prcoder-1/ATARI-SXEGS-Cartridge/photos/Black Cartridge Back.jpg

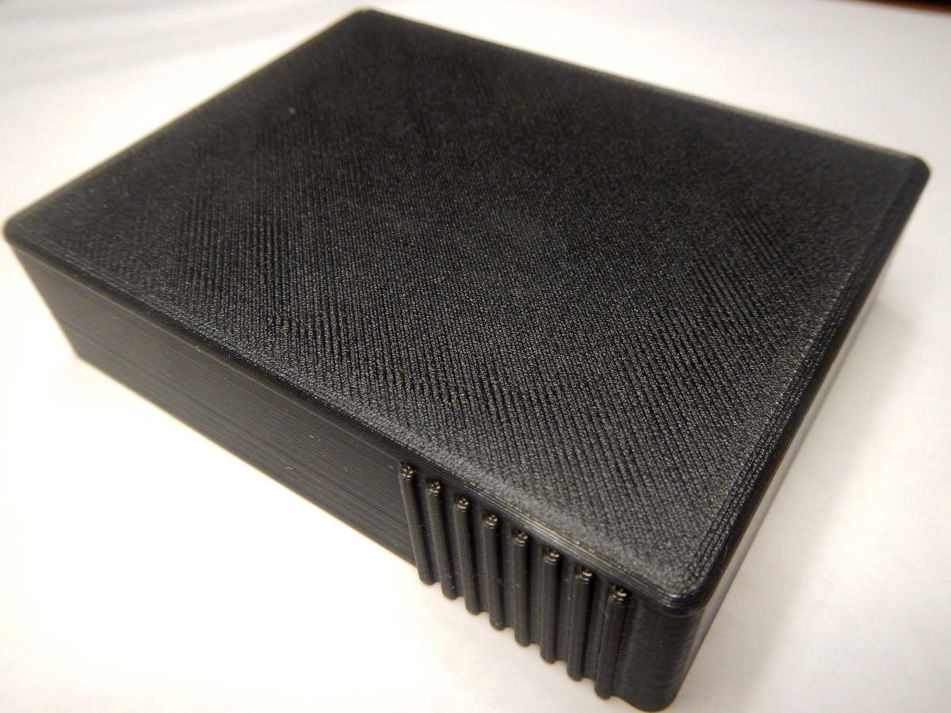
photos/Black Cartridge Back.jpg
