prcoder-1/ATARI-SXEGS-Cartridge/photos/Black Cartridge Cover.jpg

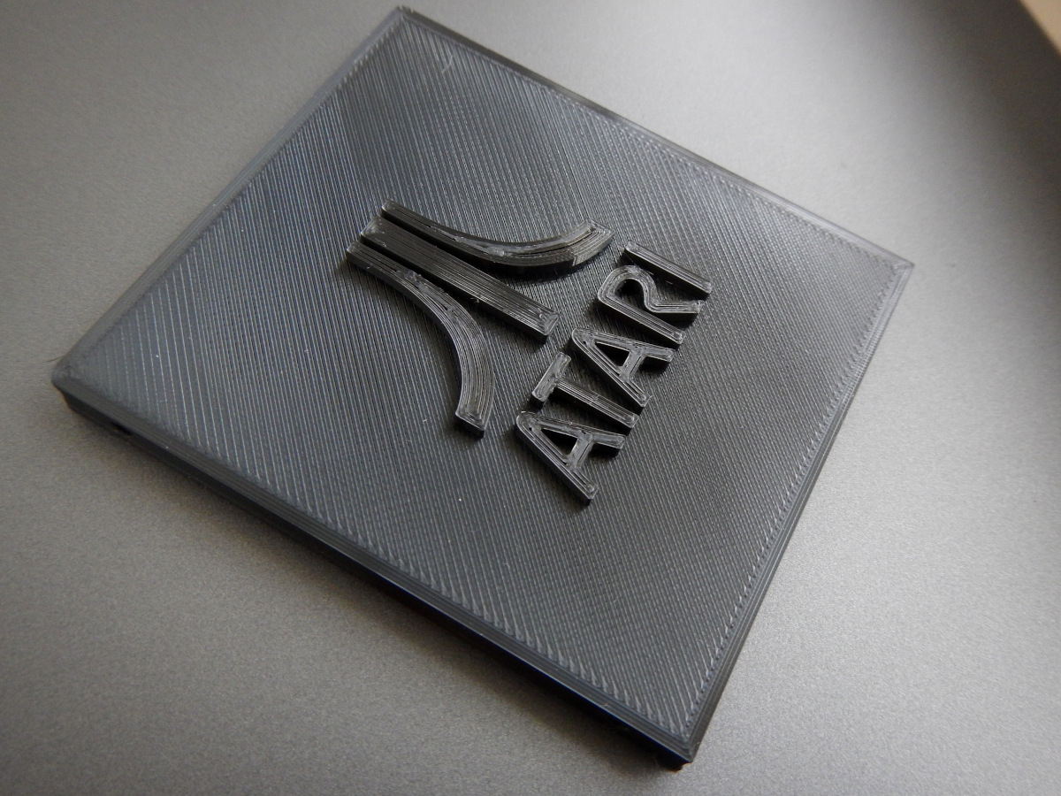
photos/Black Cartridge Cover.jpg
