prcoder-1/ATARI-SXEGS-Cartridge/photos/Blue Box Inside.jpg

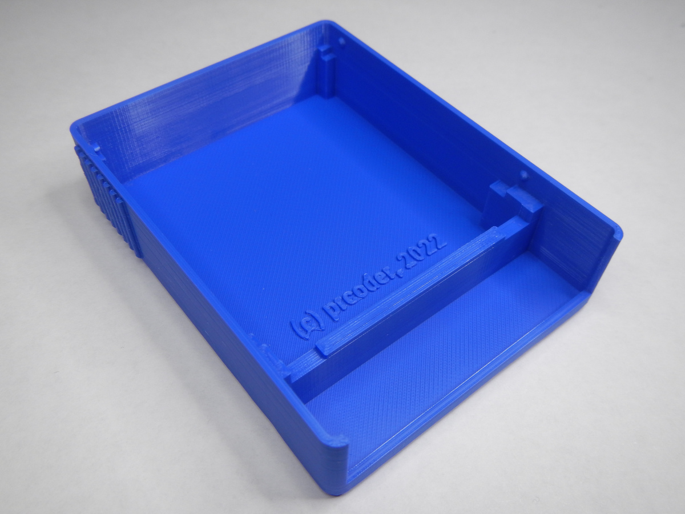
photos/Blue Box Inside.jpg
