prcoder-1/ATARI-SXEGS-Cartridge/photos/Blue Housing.jpg

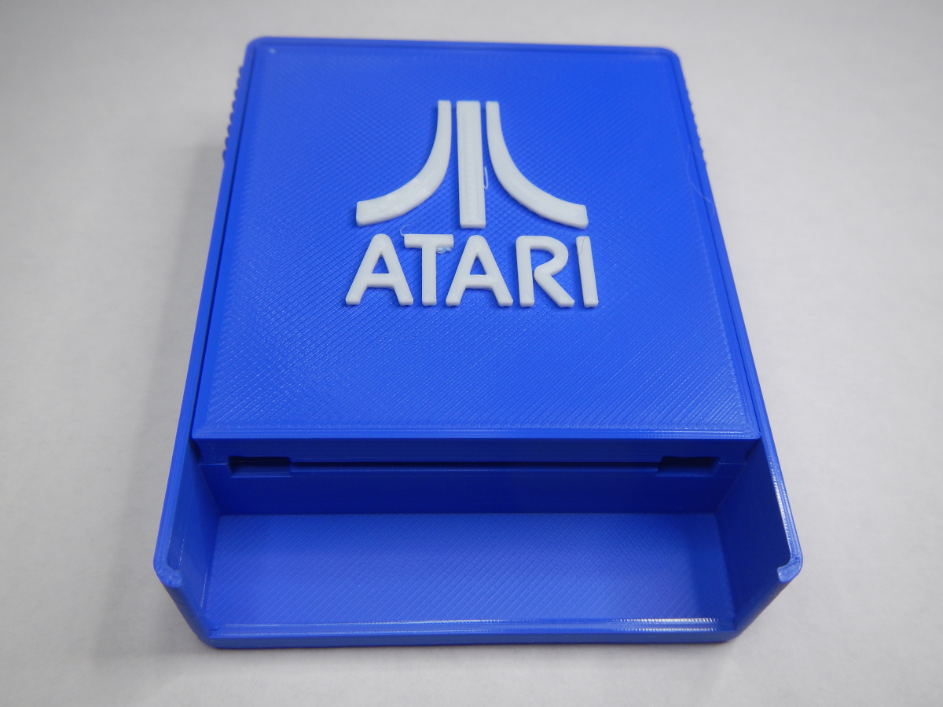
photos/Blue Housing.jpg
