prcoder-1/ATARI-SXEGS-Cartridge/photos/Blue PCB and Housing.jpg

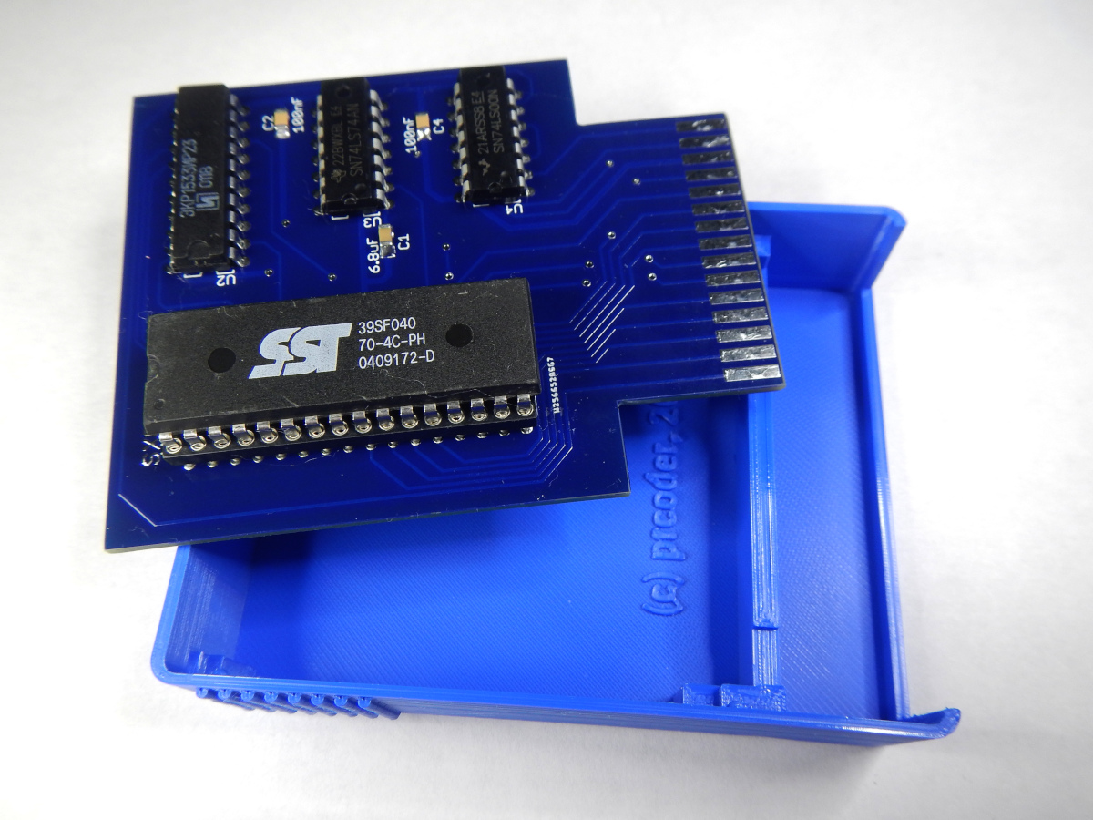
photos/Blue PCB and Housing.jpg
