prcoder-1/ATARI-SXEGS-Cartridge/photos/Blue PCB.JPG

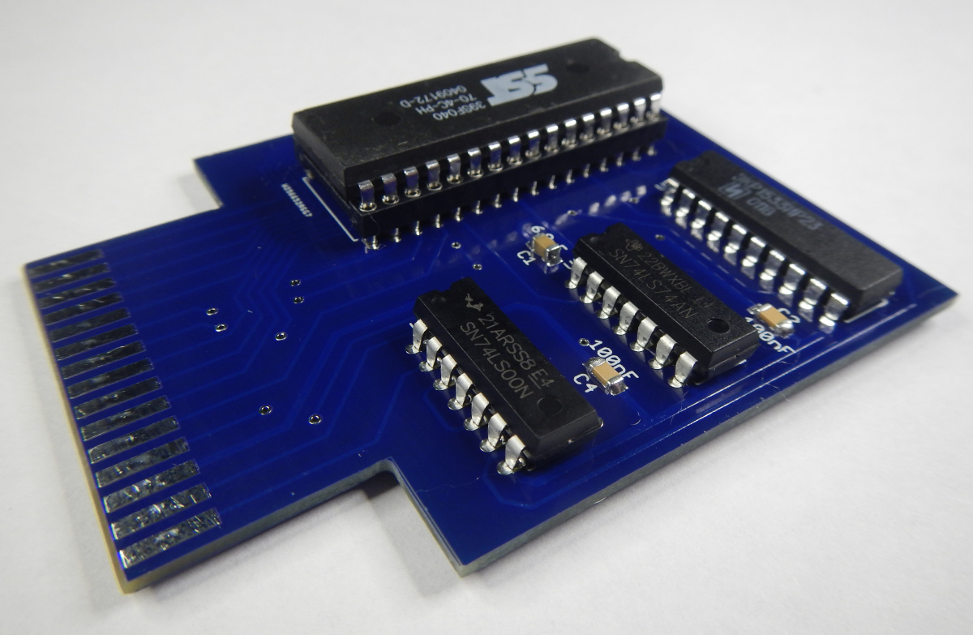
photos/Blue PCB.JPG
