prcoder-1/ATARI-SXEGS-Cartridge/photos/Board and Grey Housing.jpg

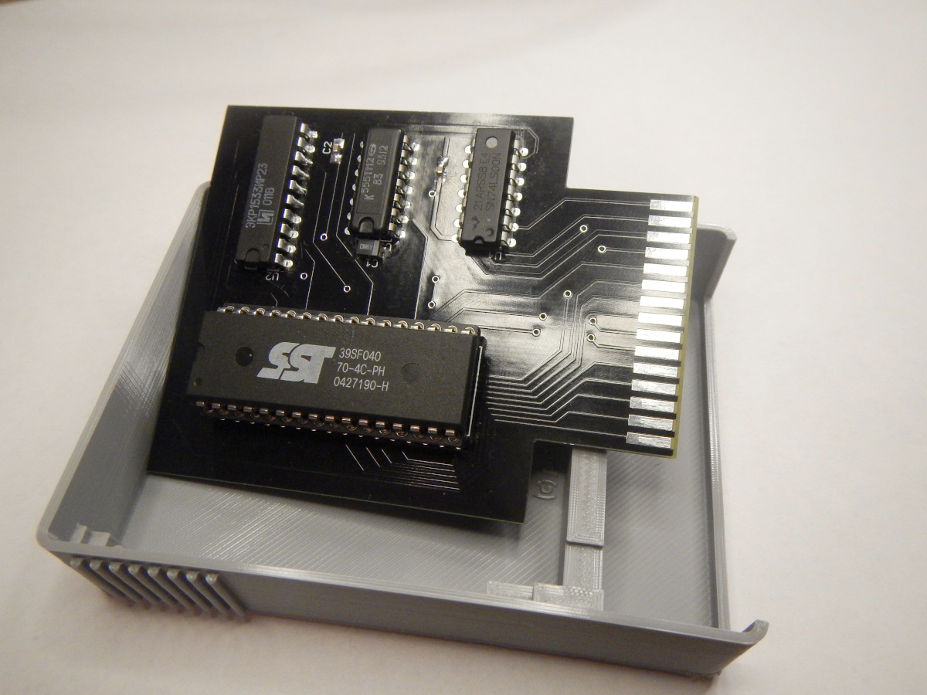
photos/Board and Grey Housing.jpg
