prcoder-1/ATARI-SXEGS-Cartridge/photos/Board in Black Housing.jpg

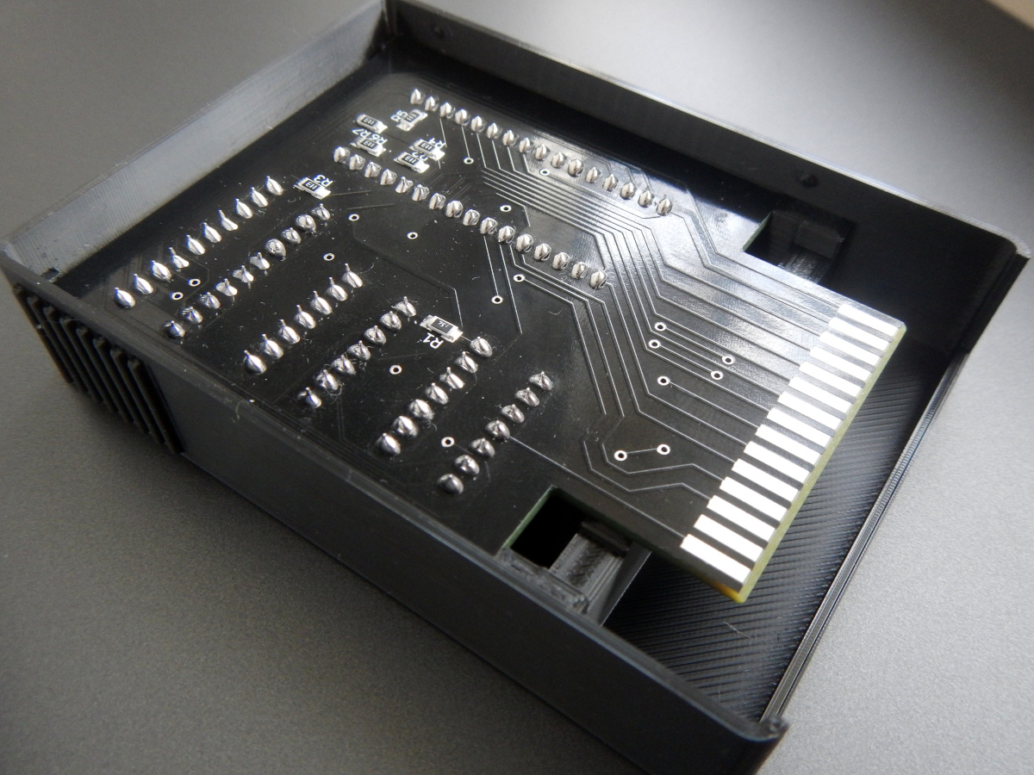
photos/Board in Black Housing.jpg
