prcoder-1/ATARI-SXEGS-Cartridge/photos/Board in Grey Housing.jpg

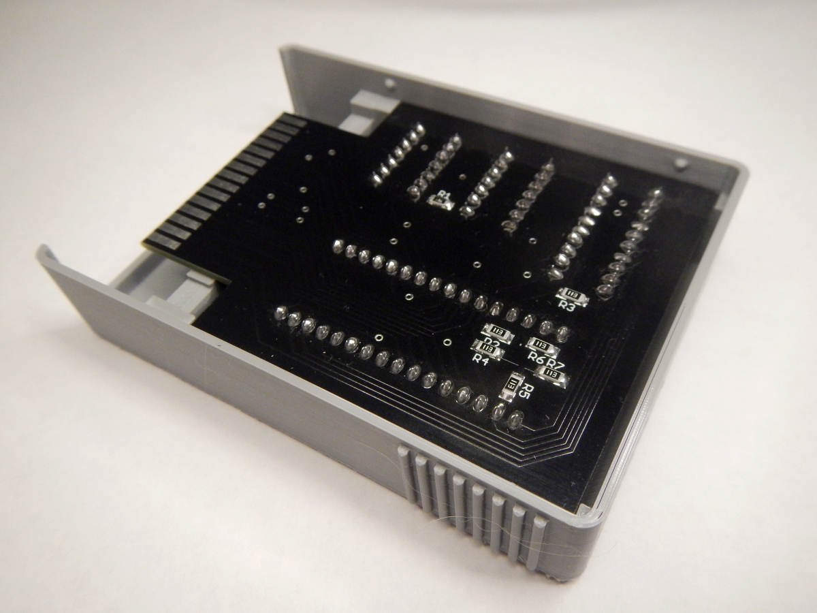
photos/Board in Grey Housing.jpg
