prcoder-1/ATARI-SXEGS-Cartridge/photos/Cartridge Dimensions.png

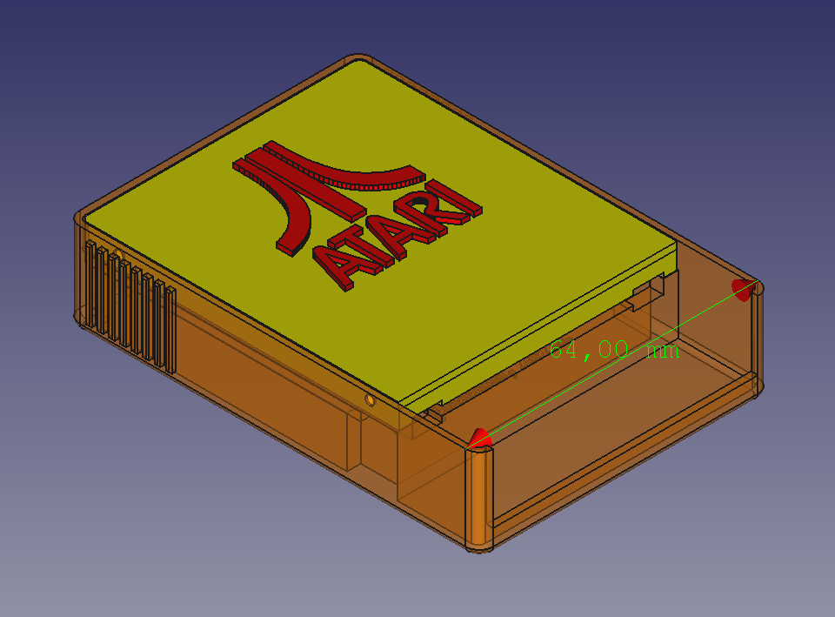
photos/Cartridge Dimensions.png
