prcoder-1/ATARI-SXEGS-Cartridge/photos/Grey Cartridge Housing.jpg

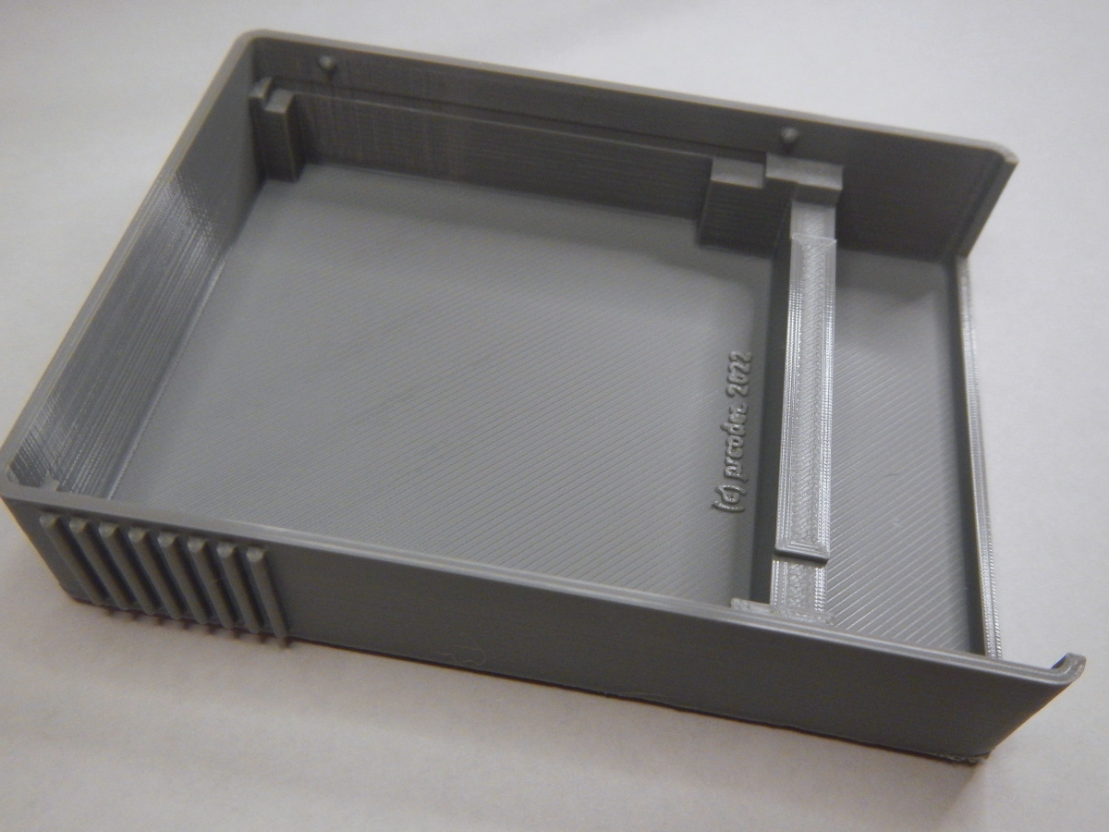
photos/Grey Cartridge Housing.jpg
