prcoder-1/ATARI-SXEGS-Cartridge/photos/Grey Cartridge in ATARI.jpg

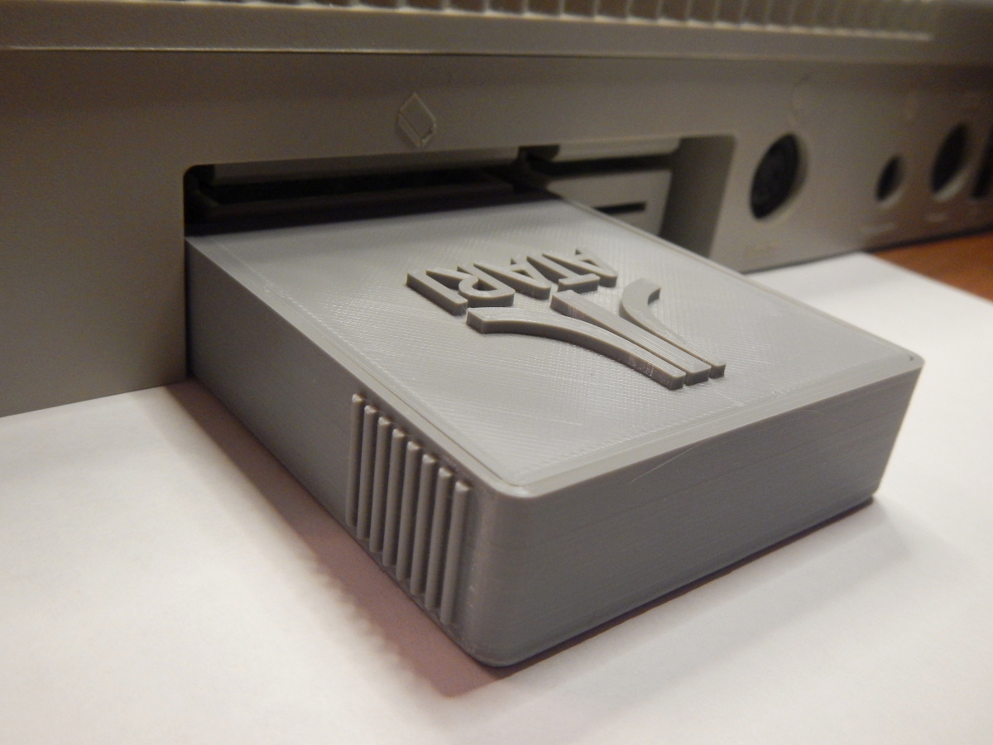
photos/Grey Cartridge in ATARI.jpg
