prcoder-1/ATARI-SXEGS-Cartridge/photos/PCB Dimensions.png

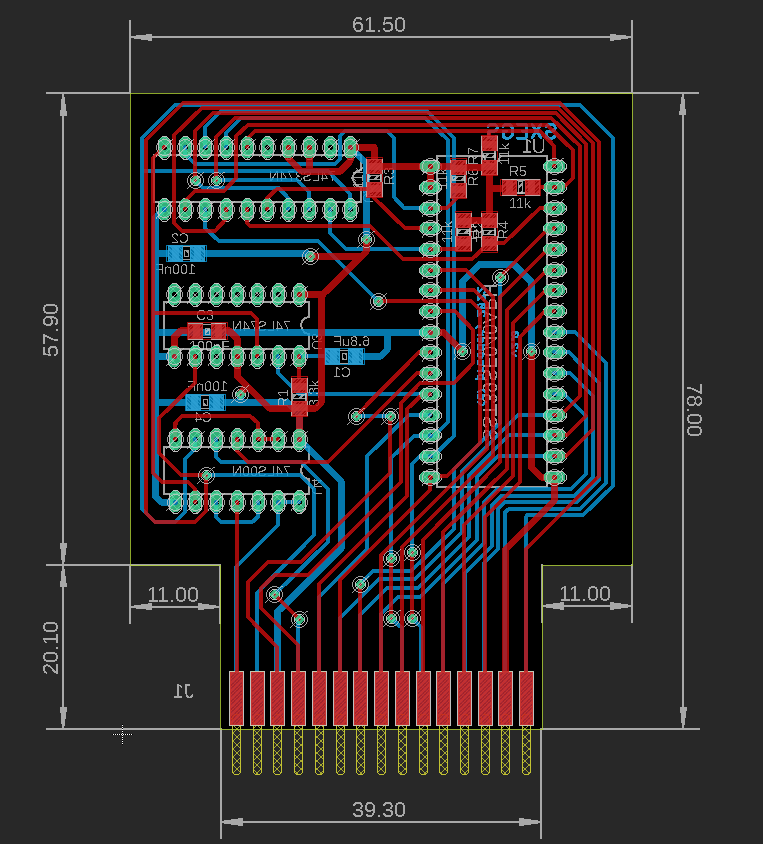
photos/PCB Dimensions.png
