prcoder-1/ATARI-SXEGS-Cartridge/photos/small/Grey Cartridge in ATARI.jpg

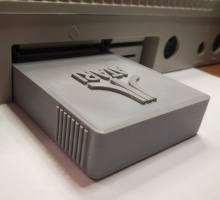
photos/small/Grey Cartridge in ATARI.jpg
