prcoder-1/ATARI-SXEGS-Cartridge/photos/Assembled PCB 1.jpg

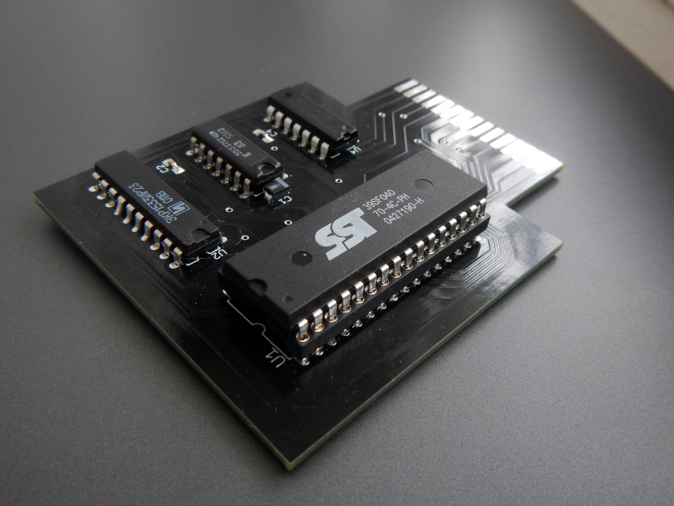
photos/Assembled PCB 1.jpg
